adamm/starman/firmware/main/buttons.c

/*
   Copyright 2022 Adam McDaniel

   Licensed under the Apache License, Version 2.0 (the "License");
   you may not use this file except in compliance with the License.
   You may obtain a copy of the License at

       http://www.apache.org/licenses/LICENSE-2.0

   Unless required by applicable law or agreed to in writing, software
   distributed under the License is distributed on an "AS IS" BASIS,
   WITHOUT WARRANTIES OR CONDITIONS OF ANY KIND, either express or implied.
   See the License for the specific language governing permissions and
   limitations under the License.
*/

#include <freertos/FreeRTOS.h>
#include <freertos/task.h>
#include <freertos/queue.h>
#include <driver/gpio.h>
#include <driver/gptimer.h>
#include <esp_log.h>
#include <string.h>

#include "buttons.h"
#include "config.h"
#include "display.h"
#include "music.h"
#include "sparkle.h"
#include "text.h"
#include "themes.h"

#define TIMER_SECONDS  1
#define TIMER_SCALE    1000000
#define BUTTON_TIMEOUT (TIMER_SECONDS * TIMER_SCALE)
 // Since the resolution is 1us, 1000000 represents 1s

static const char *TAG = "starman-buttons";

static display_t* display = NULL;
static TaskHandle_t text_task;
static void (*callback_func)(void) = NULL;
static QueueSetHandle_t evt_queue_set = NULL;
static xQueueHandle gpio_evt_queue = NULL;
static xQueueHandle timer_evt_queue = NULL;

gptimer_handle_t gptimer = NULL;
gptimer_config_t timer_config = {};

static void IRAM_ATTR gpio_isr_handler(void* arg) {
    uint32_t gpio_num = (uint32_t) arg;

    xQueueSendFromISR(gpio_evt_queue, &gpio_num, NULL);
}


static bool timer_alarm_callback(gptimer_handle_t timer, const gptimer_alarm_event_data_t *edata, void *user_ctx) {
    uint64_t counter = 0;

    gptimer_get_raw_count(timer, &counter);

    // ets_printf("Timer Alert!\n");
    xQueueSendFromISR(timer_evt_queue, &counter, NULL);

    return pdTRUE;
}


static void scroll_theme_text() {
    while(1) {
        text_scroll(display);
        display_update_leds(display);
        vTaskDelay(100 / portTICK_RATE_MS);
    }
}


static void gpio_button_task() {
    QueueSetMemberHandle_t activated_evt_queue;
    uint32_t io_num;
    static bool prev_state = false;
    static bool theme_select_mode = false;
    static bool timer_overrides_button = false;

    for(;;) {
        activated_evt_queue = xQueueSelectFromSet(evt_queue_set, portMAX_DELAY);
        if(activated_evt_queue == gpio_evt_queue) {
            xQueueReceive(gpio_evt_queue, &io_num, 0);

            // The button GPIO is active-low
            bool now_state = !gpio_get_level(io_num);
            bool button_released = !now_state;
            bool button_changed = (now_state != prev_state);

            if (now_state != prev_state) {
                if (now_state == 1) {
                    button_released = 0;
                    gptimer_start(gptimer);
                }
                else {
                    button_released = 1;
                    gptimer_stop(gptimer);
                    gptimer_set_raw_count(gptimer, 0);

                }
            }
            prev_state = now_state;
            printf("GPIO[%ld] intr, val: %d\n", io_num, now_state);

            // In normal mode, and user makes a short button press, play the game.
            // In normal mode, and user makes a long button press, go into theme select mode.
            // In theme-select mode, and user makes a short button press, rotate through the theme options.
            // In theme-select mode, and user makes a long button press, save the theme setting and return to normal mode.

            // Verify the button was just changed, becuase sometimes the GPIO
            // fires multiple high/button-release events in a row, despite not
            // actually changing state.
            if (button_released && button_changed && !timer_overrides_button) {
                if (theme_select_mode) {
                    char theme_text[10] = {0};

                    ESP_LOGI(TAG, "Selecting next theme");

                    // make a single beep: medium note
                    music_amp_unmute();
                    music_play_note(G5, 0.1);
                    music_amp_mute();

                    // select the next theme, save it, and scroll its name on the display
                    config_theme++;
                    if (config_theme >= TOTAL_THEMES_AVAILABLE)
                        config_theme = 0;
                    config_set_theme(config_theme);

                    sprintf(theme_text, " %s ", themes[config_theme].title);
                    text_write_string(display, theme_text);
                    display_update_leds(display);
                    // Text should continue to scroll from the established scroll_theme_text() task
                }
                else {
                    // Execute normal button press functionality.
                    // ie, play the game!
                    ESP_LOGI(TAG, "Calling main program");
                    if (callback_func != NULL) {
                        buttons_stop();
                        callback_func();
                        buttons_start();
                    }
                }
            }
            else {
                // The timer has overrideen the button event, the next button
                // event will be allowed (unless the timer event fires again)
                timer_overrides_button = false;
            }
        }
        else if(activated_evt_queue == timer_evt_queue) {
            // The button-hold timer has fired.  Switch states!
            theme_select_mode = !theme_select_mode;

            // Ignore next button press.  This ensures that when the button is
            // released after timer fires, a short-press isn't also recorded.
            timer_overrides_button = true;
            // Also stop the timer to ensure continuing to hold down the button
            // past the alert doesn't cycle theme-select mode in and out
            gptimer_stop(gptimer);
            gptimer_set_raw_count(gptimer, 0);

            // If entering theme-select mode, do two beeps: low-high notes
            // If leaving theme-select mode, do two beeps: high-low notes
            if (theme_select_mode) {
                char theme_text[15] = {0};

                ESP_LOGI(TAG, "Entering theme-select mode");
                music_amp_unmute();
                music_play_note(C5, 0.2);
                music_play_note(C6, 0.2);
                music_amp_mute();

                // Clear the display and show the currently selected theme
                sparkle_stop();
                display = calloc(1, sizeof(display_t));
                memset(display, 0, sizeof(display_t));

                sprintf(theme_text, " %s ", themes[config_theme].title);
                text_write_string(display, theme_text);
                display_update_leds(display);

                // Set a timer that calles text_scroll(display) to rotate through the name
                xTaskCreate(scroll_theme_text, "theme", 8192, NULL, 5, &text_task);

                // TODO: start a timer to auto-exit theme-select mode after a five seconds of inactivty.
            }
            else {
                ESP_LOGI(TAG, "Leaving theme-select mode");
                music_amp_unmute();
                music_play_note(C6, 0.2);
                music_play_note(C5, 0.2);
                music_amp_mute();

                // Stop scrolling and reset the display to the sparkle routine
                vTaskDelete(text_task);
                // Give the scroller a chance to complete its final update
                vTaskDelay(150 / portTICK_RATE_MS);
                free(display);
                display = NULL;
                sparkle_start();
            }
        }
    }
}


void buttons_play_callback(void (*callback)(void)) {
    callback_func = callback;
}


void buttons_init(void) {
    timer_evt_queue = xQueueCreate(10, sizeof(uint32_t));
    gpio_evt_queue = xQueueCreate(10, sizeof(uint32_t));
    evt_queue_set = xQueueCreateSet(20);
    xQueueAddToSet(timer_evt_queue, evt_queue_set);
    xQueueAddToSet(gpio_evt_queue, evt_queue_set);

    timer_config.clk_src = GPTIMER_CLK_SRC_DEFAULT;
    timer_config.direction = GPTIMER_COUNT_UP;
    timer_config.resolution_hz = 1 * 1000 * 1000;

    gptimer_new_timer(&timer_config, &gptimer);

    gptimer_alarm_config_t alarm_config = {
        .reload_count = 0,      // When the alarm event occurs, the timer will automatically reload to 0
        .alarm_count = BUTTON_TIMEOUT,
        .flags.auto_reload_on_alarm = true, // Enable auto-reload function
    };

    gptimer_set_alarm_action(gptimer, &alarm_config);

    gptimer_set_raw_count(gptimer, 0);

    gptimer_event_callbacks_t cbs = {
        .on_alarm = timer_alarm_callback, // Call the user callback function when the alarm event occurs
    };
    gptimer_register_event_callbacks(gptimer, &cbs, NULL);
    gptimer_enable(gptimer);

    // Timer is actually started when the button is pressed; stopped when its released or alarm triggered

    gpio_config_t io_conf = {};

    io_conf.intr_type = GPIO_INTR_ANYEDGE;
    io_conf.pin_bit_mask = (1ULL << PLAY_GAME_GPIO);
    io_conf.mode = GPIO_MODE_INPUT;
    io_conf.pull_up_en = 1;  // This shouldn't be necessary as R2 is doing this -- verify

    gpio_config(&io_conf);
    xTaskCreate(gpio_button_task, "gpio_button_task", 8196, NULL, 10, NULL);

    gpio_install_isr_service(ESP_INTR_FLAG_LOWMED);

    ESP_LOGI(TAG, "Init success");
}


void buttons_start() {
    gpio_isr_handler_add(PLAY_GAME_GPIO, gpio_isr_handler, (void*) PLAY_GAME_GPIO);
    ESP_LOGI(TAG, "Starting button handler");
}


void buttons_stop() {
    gpio_isr_handler_remove(PLAY_GAME_GPIO);
    ESP_LOGI(TAG, "Stopped button handler");
}
