adamm/starman/firmware/main/patterns.h

/*
   Copyright 2022 Adam McDaniel

   Licensed under the Apache License, Version 2.0 (the "License");
   you may not use this file except in compliance with the License.
   You may obtain a copy of the License at

       http://www.apache.org/licenses/LICENSE-2.0

   Unless required by applicable law or agreed to in writing, software
   distributed under the License is distributed on an "AS IS" BASIS,
   WITHOUT WARRANTIES OR CONDITIONS OF ANY KIND, either express or implied.
   See the License for the specific language governing permissions and
   limitations under the License.
*/

#ifndef PATTERNS_H
#define PATTERNS_H

// Techncially the star is 16 LEDs wide and 15 LEDs tall, and is only 144 LEDs total. 
// In order to make the math for rotation and flipping easier, we assume it's 16x16 square.
// Thus, the top row of the pattern will be ignored when updating the lights.
// 
// In other words, if XX is a LED, data outside of XX will be thrown away:
// 
//      1  2  3  4  5  6  7  8  9 10 11 12 13 14 15 16
//  1  __ __ __ __ __ __ __ __ __ __ __ __ __ __ __ __
//  2  __ __ __ __ __ __ __ XX XX __ __ __ __ __ __ __
//  3  __ __ __ __ __ __ XX XX XX XX __ __ __ __ __ __
//  4  __ __ __ __ __ __ XX XX XX XX __ __ __ __ __ __
//  5  __ __ __ __ __ XX XX XX XX XX XX __ __ __ __ __
//  6  XX XX XX XX XX XX XX XX XX XX XX XX XX XX XX XX
//  7  XX XX XX XX XX XX XX XX XX XX XX XX XX XX XX XX
//  8  __ XX XX XX XX XX XX XX XX XX XX XX XX XX XX __
//  9  __ __ XX XX XX XX XX XX XX XX XX XX XX XX __ __
// 10  __ __ __ XX XX XX XX XX XX XX XX XX XX __ __ __
// 11  __ __ XX XX XX XX XX XX XX XX XX XX XX XX __ __
// 12  __ __ XX XX XX XX XX XX XX XX XX XX XX XX __ __
// 13  __ XX XX XX XX XX XX XX XX XX XX XX XX XX XX __
// 14  __ XX XX XX XX XX XX __ __ XX XX XX XX XX XX __
// 15  XX XX XX XX XX __ __ __ __ __ __ XX XX XX XX XX
// 16  XX XX XX __ __ __ __ __ __ __ __ __ __ XX XX XX
//

struct pattern {
    uint8_t height;
    uint8_t width;
    uint8_t data[];
} typedef pattern_t;

static const pattern_t castle = {
    16, 16, {
          1,   1,   1,   1,   1,   1,   1,   1,   1,   1,   1,   1,   1,   1,   1,   1,
          1,   1,   1,   1,   1,   1,   1,   1,   1,   1,   1,   1,   1,   1,   1,   1,
          1,   1,   1,  32, 128, 128, 128, 128,   1,   1,   1,  32, 128, 128, 128, 128,
          1,   1,   1,  32, 128, 128, 128,  64,   1,   1,   1,  32, 128, 128, 128,  64,
          1,   1,   1,  32, 128, 128, 128,  64,   1,   1,   1,  32, 128, 128, 128,  64,
          1,   1,   1,  32,  32,  32,  32,  32,   1,   1,   1,  32,  32,  32,  32,  32,
          1,   1,   1,   1,   1,   1,   1,   1,   1,   1,   1,   1,   1,   1,   1,   1,
        128, 128, 128, 128,   1,   1,   1,  32, 128, 128, 128, 128,   1,   1,   1,  32,
        128, 128, 128,  64,   1,   1,   1,  32, 128, 128, 128,  64,   1,   1,   1,  32,
        128, 128, 128,  64,   1,   1,   1,  32, 128, 128, 128,  64,   1,   1,   1,  32,
         32,  32,  32,  32,   1,   1,   1,  32,  32,  32,  32,  32,   1,   1,   1,  32,
          1,   1,   1,   1,   1,   1,   1,   1,   1,   1,   1,   1,   1,   1,   1,   1,
          1,   1,   1,  32, 128, 128, 128, 128,   1,   1,   1,  32, 128, 128, 128, 128,
          1,   1,   1,  32, 128, 128, 128,  64,   1,   1,   1,  32, 128, 128, 128,  64,
          1,   1,   1,  32, 128, 128, 128,  64,   1,   1,   1,  32, 128, 128, 128,  64,
          1,   1,   1,  32,  32,  32,  32,  32,   1,   1,   1,  32,  32,  32,  32,  32,
    }
};

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
void patterns_random();
void patterns_siren();
void patterns_sprinkles();
void patterns_spiral();
void patterns_sweep();
void patterns_swirl();
void patterns_swipe();
void patterns_swoosh();
void patterns_starman();
void patterns_swoop();
void patterns_thump();
void patterns_waves();

#endif
