adamm/starman/firmware/main/patterns_gol.h

/*
   Copyright 2022 Adam McDaniel

   Licensed under the Apache License, Version 2.0 (the "License");
   you may not use this file except in compliance with the License.
   You may obtain a copy of the License at

       http://www.apache.org/licenses/LICENSE-2.0

   Unless required by applicable law or agreed to in writing, software
   distributed under the License is distributed on an "AS IS" BASIS,
   WITHOUT WARRANTIES OR CONDITIONS OF ANY KIND, either express or implied.
   See the License for the specific language governing permissions and
   limitations under the License.
*/

#ifndef PATTERNS_GOL_H
#define PATTERNS_GOL_H

#include "config.h"
#include "patterns.h"

// Note: The Game Of Life grid is larger than the display area to allow for more complex designs.

static const uint8_t gol_cross_2[GOL_GRID_HEIGHT][GOL_GRID_WIDTH] = {
    {   0,   0,   0,   0,   0,   0,   0,   0,   0,   0,   0,   0,   0,   0,   0,   0,   0,   0,   0,   0,   0,   0,   0,   0 },
    {   0,   0,   0,   0,   0,   0,   0,   0,   0,   0,   0,   0,   0,   0,   0,   0,   0,   0,   0,   0,   0,   0,   0,   0 },
    {   0,   0,   0,   0,   0,   0,   0,   0,   0,   0,   0,   0,   0,   0,   0,   0,   0,   0,   0,   0,   0,   0,   0,   0 },
    {   0,   0,   0,   0,   0,   0,   0,   0,   0,   0,   0,   0,   0,   0,   0,   0,   0,   0,   0,   0,   0,   0,   0,   0 },
    {   0,   0,   0,   0,   0,   0,   0,   0,   0,   0,   0,   0,   0,   0,   0,   0,   0,   0,   0,   0,   0,   0,   0,   0 },
    {   0,   0,   0,   0,   0,   0,   0,   0,   0,   0,   0,   0,   0,   0,   0,   0,   0,   0,   0,   0,   0,   0,   0,   0 },
    {   0,   0,   0,   0,   0,   0,   0,   0,   0,   0,   0,   0,   0,   0,   0,   0,   0,   0,   0,   0,   0,   0,   0,   0 },
    {   0,   0,   0,   0,   0,   0,   0,   0,   0,   0,   0,   0,   0,   0,   0,   0,   0,   0,   0,   0,   0,   0,   0,   0 },
    {   0,   0,   0,   0,   0,   0,   0,   0,   0,   0,   0,   0,   0,   0,   0,   0,   0,   0,   0,   0,   0,   0,   0,   0 },
    {   0,   0,   0,   0,   0,   0,   0,   0,   0,   0,   0,   0,   0,   0,   0,   0,   0,   0,   0,   0,   0,   0,   0,   0 },
    {   0,   0,   0,   0,   0,   0,   0, 255, 255, 255, 255,   0, 255, 255, 255, 255,   0,   0,   0,   0,   0,   0,   0,   0 },
    {   0,   0,   0,   0,   0,   0,   0, 255,   0,   0, 255,   0, 255,   0,   0, 255,   0,   0,   0,   0,   0,   0,   0,   0 },
    {   0,   0,   0,   0,   0, 255, 255, 255,   0,   0, 255, 255, 255,   0,   0, 255, 255, 255,   0,   0,   0,   0,   0,   0 },
    {   0,   0,   0,   0,   0, 255,   0,   0,   0,   0,   0,   0,   0,   0,   0,   0,   0, 255,   0,   0,   0,   0,   0,   0 },
    {   0,   0,   0,   0,   0, 255,   0,   0,   0,   0,   0,   0,   0,   0,   0,   0,   0, 255,   0,   0,   0,   0,   0,   0 },
    {   0,   0,   0,   0,   0, 255, 255, 255,   0,   0,   0,   0,   0,   0,   0, 255, 255, 255,   0,   0,   0,   0,   0,   0 },
    {   0,   0,   0,   0,   0,   0,   0, 255,   0,   0,   0,   0,   0,   0,   0, 255,   0,   0,   0,   0,   0,   0,   0,   0 },
    {   0,   0,   0,   0,   0, 255, 255, 255,   0,   0,   0,   0,   0,   0,   0, 255, 255, 255,   0,   0,   0,   0,   0,   0 },
    {   0,   0,   0,   0,   0, 255,   0,   0,   0,   0,   0,   0,   0,   0,   0,   0,   0, 255,   0,   0,   0,   0,   0,   0 },
    {   0,   0,   0,   0,   0, 255,   0,   0,   0,   0,   0,   0,   0,   0,   0,   0,   0, 255,   0,   0,   0,   0,   0,   0 },
    {   0,   0,   0,   0,   0, 255, 255, 255,   0,   0, 255, 255, 255,   0,   0, 255, 255, 255,   0,   0,   0,   0,   0,   0 },
    {   0,   0,   0,   0,   0,   0,   0, 255,   0,   0, 255,   0, 255,   0,   0, 255,   0,   0,   0,   0,   0,   0,   0,   0 },
    {   0,   0,   0,   0,   0,   0,   0, 255, 255, 255, 255,   0, 255, 255, 255, 255,   0,   0,   0,   0,   0,   0,   0,   0 },
    {   0,   0,   0,   0,   0,   0,   0,   0,   0,   0,   0,   0,   0,   0,   0,   0,   0,   0,   0,   0,   0,   0,   0,   0 },
    {   0,   0,   0,   0,   0,   0,   0,   0,   0,   0,   0,   0,   0,   0,   0,   0,   0,   0,   0,   0,   0,   0,   0,   0 },
    {   0,   0,   0,   0,   0,   0,   0,   0,   0,   0,   0,   0,   0,   0,   0,   0,   0,   0,   0,   0,   0,   0,   0,   0 },
    {   0,   0,   0,   0,   0,   0,   0,   0,   0,   0,   0,   0,   0,   0,   0,   0,   0,   0,   0,   0,   0,   0,   0,   0 },
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
};

// Global functions defined in patterns.c
void patterns_gol_cross_2();
void patterns_gol_galaxy();
void patterns_gol_sprinkles();
void patterns_gol_four_blinkers_four_blocks();
void patterns_gol_pentadecathlon();

#endif
