adamm/starman/smbw.h

// Playtune bytestream for file "overworld-2.mid" created by MIDITONES V1.17 on Wed Dec  1 13:55:52 2021
// command line: /Users/adamm/git/miditones/miditones -d -pi -s1 -t4 overworld-2 
const unsigned char PROGMEM overworld [] = {
'P','t', 6, 0x00, 0x00,  4, // (Playtune file header)
0x90,45, 0x91,41, 0x92,71, 0,100, 0x92,69, 0,66, 0x80, 0x81, 0,33, 0x90,65, 0x82, 0,100, 0x90,45, 0x91,71, 0x92,41, 
0,200, 0x91,69, 0,33, 0x80, 0x82, 0,66, 0x90,65, 0x81, 0,100, 0x90,44, 0x91,40, 0x92,64, 0,166, 0x82, 0,33, 
0x90,76, 0x91,68, 0,100, 0x80, 0x81, 0,100, 0x90,76, 0x91,68, 0,100, 0x80, 0x81, 1,44, 0x90,57, 0,100, 0x90,69, 
0x91,61, 0x92,33, 0,100, 0x90,64, 0x91,57, 0x82, 0,100, 0x90,64, 0x91,67, 0,100, 0x90,37, 0x91,61, 0x92,69, 0,100, 
0x80, 0,100, 0x90,57, 0x81, 0x82, 0,100, 0x90,40, 0x91,61, 0x92,69, 0,100, 0x90,57, 0x91,64, 0x82, 0,100, 0x90,64, 
0x91,67, 0,100, 0x90,37, 0x91,69, 0x92,61, 0,100, 0x80, 0,100, 0x90,57, 0x91,61, 0x82, 0,100, 0x92,33, 0,100, 
0x82, 0,66, 0x80, 0x81, 0,33, 0x90,40, 0,100, 0x90,57, 0,100, 0x90,38, 0x91,62, 0x92,69, 0,100, 0x90,57, 0x81, 
0x82, 0,100, 0x90,65, 0,100, 0x90,33, 0x91,62, 0x92,69, 0,100, 0x80, 0,100, 0x90,57, 0x81, 0x82, 0,66, 0x91,38, 
0,33, 0x90,69, 0x92,62, 0,66, 0x81, 0,33, 0x90,57, 0x82, 0,100, 0x90,62, 0x91,65, 0,100, 0x90,62, 0x91,69, 
0x92,33, 0,100, 0x82, 0,100, 0x90,57, 0x91,62, 0,100, 0x92,33, 0,100, 0x82, 0,33, 0x80, 0x81, 0,66, 0x90,31, 
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
1,187, 0x80, 0,6, 0x90,81, 1,37, 0x80, 0,6, 0x90,86, 1,37, 0x80, 0,6, 0x90,91, 4,26, 0x80, 0x81, 0x82, 
0x83, 0xf0};
// This score contains 113 bytes, and 4 tone generators are used.
// 4 notes had to be skipped.
