adamm/starman/Music.h

#include <Arduino.h>

// Playtune bytestream for file "overworld.mid" created by MIDITONES V1.17 on Sat Nov 27 22:43:04 2021
// command line: ./miditones -d -pi -s1 -t4 overworld 
const unsigned char PROGMEM overworld [] = {
'P','t', 6, 0x00, 0x00,  4, // (Playtune file header)
0x90,86, 0x91,72, 0x92,81, 0x93,58, 0x90,82, 0x91,77, 0x92,69, 0x93,53, 1,84, 0x90,77, 0x91,69, 0x92,72, 
0x93,50, 0,113, 0x90,76, 0x91,67, 0x92,71, 0x93,48, 0,113, 0x80, 0x81, 0x82, 0x83, 0,113, 0x90,77, 0x91,69, 0x92,72, 
0x93,50, 0,113, 0x90,79, 0x91,71, 0x92,74, 0x93,52, 2,56, 0x93,41, 0x90,81, 0x91,72, 0x92,41, 0,113, 0x80, 0x81, 
0,56, 0x83, 0,56, 0x90,72, 0x91,81, 0x82, 0,56, 0x80, 0x81, 0,56, 0x90,72, 0x91,81, 0,56, 0x80, 0x81, 0,56, 
0x93,38, 0x90,81, 0x91,72, 0x92,38, 0,113, 0x80, 0x81, 0,56, 0x83, 0,56, 0x90,81, 0x91,72, 0x82, 0,56, 0x80, 0x81, 
0,56, 0x90,81, 0x91,72, 0,56, 0x80, 0x81, 0,56, 0x93,43, 0x90,74, 0x91,82, 0x92,43, 0,113, 0x80, 0x81, 0,56, 
0x83, 0,56, 0x90,74, 0x91,82, 0x82, 0,56, 0x80, 0x81, 0,56, 0x90,74, 0x91,82, 0,56, 0x80, 0x81, 0,56, 0x93,36, 
0x90,73, 0x91,82, 0x92,36, 0,113, 0x80, 0x81, 0,56, 0x83, 0,56, 0x90,73, 0x91,82, 0x82, 0,56, 0x80, 0x81, 0,56, 
0x90,73, 0x91,82, 0,56, 0x80, 0x81, 0,56, 0x93,41, 0x90,81, 0x91,72, 0x92,41, 0,113, 0x80, 0x81, 0,56, 0x83, 0,56, 
0x90,81, 0x91,72, 0x82, 0,56, 0x80, 0x81, 0,56, 0x90,81, 0x91,72, 0,56, 0x80, 0x81, 0,56, 0x93,38, 0x90,72, 0x91,81, 
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
1,144, 0,4, 0x91,43,64, 0,45, 0,50, 0,50, 0,50, 0,51, 0,51, 0,51, 0,51, 0x90,64,56, 
0x91,48,64, 0x92,72,70, 3,60, 0x80, 0x81, 0x82, 0xf0};
// This score contains 471 bytes, and 3 tone generators are used.
