adamm/starman/main/status.c

#include <driver/gpio.h>
#include <freertos/FreeRTOS.h>
#include <freertos/task.h>
#include <freertos/event_groups.h>
#include <esp_log.h>

#include "config.h"
#include "util.h"

#include "status.h"

static TaskHandle_t flashing_task;
static const char *TAG = "starman-status";

#define MAX_BRIGHTNESS 16
#define RED   MAX_BRIGHTNESS
#define GREEN MAX_BRIGHTNESS
#define BLUE  MAX_BRIGHTNESS


static void IRAM_ATTR ws2812b_bit_0() {
  gpio_set_level(STATUS_LED_GPIO, 1);

  //delay 0.4us
  asm("nop; nop;");

  gpio_set_level(STATUS_LED_GPIO, 0);

  // delay 0.85us (additional dleay happens within color_display();
  asm("nop; nop; nop; nop; nop; nop; nop; nop;"
    "nop; nop; nop; nop; nop; nop; nop; nop;"
    "nop; nop; nop; nop;");
}

static void IRAM_ATTR ws2812b_bit_1() {
  gpio_set_level(STATUS_LED_GPIO, 1);

  //delay 0.8us
  asm("nop; nop; nop; nop; nop; nop; nop; nop;"
    "nop; nop; nop; nop; nop; nop; nop; nop;"
    "nop; nop; nop; nop; nop; nop; nop; nop;"
    "nop; nop; nop; nop; nop; nop; nop; nop;"
    "nop; nop; nop; nop; nop; nop; nop; nop;"
    "nop; nop; nop; nop; nop; nop; nop; nop;"
    "nop; nop; nop; nop; nop; nop; nop; nop;");

  gpio_set_level(STATUS_LED_GPIO, 0);

  // delay 0.45us happens naturally within color_display() function
}


static uint8_t reverse(uint8_t num) {
    uint8_t tmp = 0;

    for (uint8_t i = 0; i < (sizeof(uint8_t) * 8 - 1); i++) {
       tmp |= num & 1;
       num >>= 1;
       tmp <<= 1;
    }

    return tmp;
}



static void color_display(uint8_t red, uint8_t green, uint8_t blue) {
    uint8_t i = 0;
    uint16_t color;
    portDISABLE_INTERRUPTS();

    color = reverse(green);
    for (i = 0; i < 8; i++) {
        if (color & 1)
            ws2812b_bit_1();
        else
            ws2812b_bit_0();
        color >>= 1;
    }

    color = reverse(red);
    for (i = 0; i < 8; i++) {
        if (color & 1)
            ws2812b_bit_1();
        else
            ws2812b_bit_0();
        color >>= 1;
    }

    color = reverse(blue);
    for (i = 0; i < 8; i++) {
        if (color & 1)
            ws2812b_bit_1();
        else
            ws2812b_bit_0();
        color >>= 1;
    }

    portENABLE_INTERRUPTS();
}




void status_init() {
    // One addressable LED is found on the STATUS_LED_GPIO port
    // Unfortunately RMT wont work as there aren't any timers left.
    // Instead the WS2812B is bitbanged.

    gpio_config_t io_conf = {};

    io_conf.intr_type = GPIO_INTR_DISABLE;
    io_conf.mode = GPIO_MODE_OUTPUT;
    io_conf.pin_bit_mask = (1ULL << STATUS_LED_GPIO);
    io_conf.pull_down_en = 0;
    io_conf.pull_up_en = 0;
    gpio_config(&io_conf);
    gpio_set_level(STATUS_LED_GPIO, 0);
    status_clear();

    ESP_LOGI(TAG, "Init success");
}


void status_clear() {
    ESP_LOGI(TAG, "Clear");
    color_display(0, 0, 0);
}


void status_connecting() {
    ESP_LOGI(TAG, "Connecting");
    color_display(0, 255, 0);
    vTaskDelay(500 / portTICK_RATE_MS);
    color_display(0, 0, 0);
}



void status_connected() {
    ESP_LOGI(TAG, "Connectted");
    color_display(0, 255, 0);
}



void flash_provisioning() {
    while (1) {
        // status_light->set_pixel(status_light, 0, RED, GREEN, BLUE);
        // status_light->refresh(status_light, 100);
        // gpio_set_level(STATUS_LED_GPIO, 1);
        color_display(255,255,255);
        vTaskDelay(500 / portTICK_RATE_MS);
        // status_light->clear(status_light, 50);
        color_display(0, 0, 0);
        vTaskDelay(500 / portTICK_RATE_MS);
    }
}


void status_provisioning() {
    ESP_LOGI(TAG, "Provisioning");
    xTaskCreate(flash_provisioning, "flash", 2048, NULL, 0, &flashing_task);
}


void status_provisioned() {
    ESP_LOGI(TAG, "Provisioned");
    color_display(0, 0, 0);
    vTaskDelete(flashing_task);
}


void status_error() {
    uint8_t blinks = 5;
    ESP_LOGE(TAG, "Error");
    for (uint8_t i = 0; i < blinks; i++) {
        color_display(255, 0, 0);
        delay(500);
        color_display(0, 0, 0);
        delay(500);
    }
}
