adamm/starman/firmware/main/stage.h

#pragma once

enum STAGE {
    STAGE_level_1,
    STAGE_level_2,
    STAGE_level_3,
    STAGE_level_4,
    STAGE_block,
    STAGE_1up,
    STAGE_powerup,
    STAGE_starman,
    STAGE_warning,
    STAGE_success,
    STAGE_clear,
    STAGE_death,
    STAGE_gameover,
    STAGE_fanfare,
    STAGE_ending,
};

#define NUM_STAGES 15
