adamm/starman/firmware/main/gol.c

/*
   Copyright 2022 Adam McDaniel

   Licensed under the Apache License, Version 2.0 (the "License");
   you may not use this file except in compliance with the License.
   You may obtain a copy of the License at

       http://www.apache.org/licenses/LICENSE-2.0

   Unless required by applicable law or agreed to in writing, software
   distributed under the License is distributed on an "AS IS" BASIS,
   WITHOUT WARRANTIES OR CONDITIONS OF ANY KIND, either express or implied.
   See the License for the specific language governing permissions and
   limitations under the License.
*/

#include <esp_log.h>
#include <string.h>
#include <stdlib.h>

#include "config.h"
#include "display.h"
#include "gol.h"

// An implementation of Conway's Game of Life to apply various oscillators as starman patterns


static uint8_t count_live_neighbours(int8_t grid[GOL_GRID_HEIGHT][GOL_GRID_WIDTH], int8_t y, int8_t x) {
    int8_t i, j, count = 0;
    for(i = y-1; i <= y+1; i++){
        for(j = x-1; j <= x+1; j++){
            if((i== y && j == x) || (i < 0 || j < 0) || ( i >= GOL_GRID_HEIGHT || j >= GOL_GRID_WIDTH)) {
                continue;
            }
            if(grid[i][j] == 1){
                count++;
            }
        }
    }
    return count;
}


void gol_next_generation(display_t *display) {
    int8_t y, x;
    int8_t this_gen[GOL_GRID_HEIGHT][GOL_GRID_WIDTH] = { 0 };
    int8_t next_gen[GOL_GRID_HEIGHT][GOL_GRID_WIDTH] = { 0 };

    for (y = 0; y < GOL_GRID_HEIGHT; y++) {
        for (x = 0; x < GOL_GRID_WIDTH; x++) {
            if (display->grid[y][x] > 0)
                this_gen[y][x] = 1;
        }
    }

    for (y = 0; y < GOL_GRID_HEIGHT; y++) {
        for (x = 0; x < GOL_GRID_WIDTH; x++) {
            int8_t count = count_live_neighbours(this_gen, y, x);
            if (this_gen[y][x] == 1 && (count == 2 || count == 3)) {
                next_gen[y][x] = 1;
            }
            else if (this_gen[y][x] == 0 && count == 3) {
                next_gen[y][x] = 1;
            }
            else {
                next_gen[y][x] = 0;
            }
        }
    }
 
    memset(display->overlay, 0, DISPLAY_LIGHTS_TOTAL_AREA);
    for (y = 0; y < DISPLAY_LIGHTS_HEIGHT; y++) {
        for (x = 0; x < DISPLAY_LIGHTS_WIDTH; x++) {
            if (next_gen[y+GOL_GRID_OFFSET_Y][x+GOL_GRID_OFFSET_X] > 0)
                display->overlay[y][x] = 255;
        }
    }

    memcpy(display->grid, next_gen, GOL_GRID_TOTAL_AREA);
}
